lorentzfactr/Temp-Hum-DAQ/Temp-Humidity-DAQ-LorentzFactr/dontlook.h

//A secret area to store your credentials




























const char host[ ]        = "192.168.x.x";         // your local host server
const char* ssid          = "";                    // SSID of local network---------------------USER Input here
const char* password      = "";                    // Password on network -----------------------------------------------------
